GaganDruvakumara/DJ-Controller/CAD Files/3D Print/RotaryEncoderKnob 2x.step

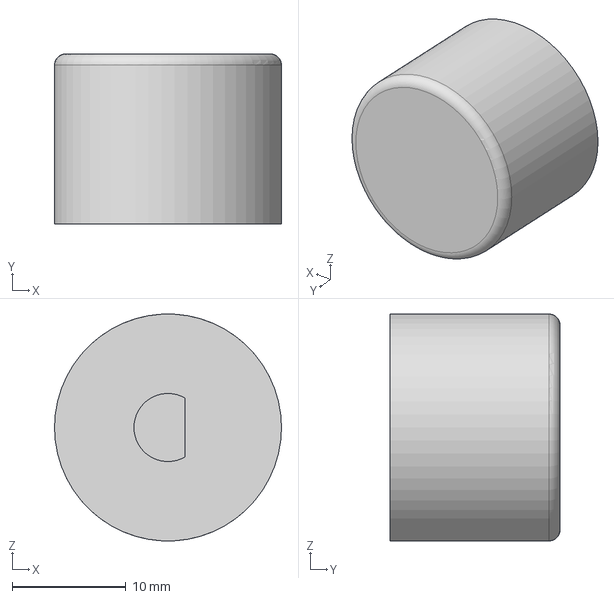
[picture p16: CAD file, 2026-06-20]
CAD Files/3D Print/RotaryEncoderKnob 2x.step
20.0 x 15.0 x 20.0 mm
