GaganDruvakumara/DJ-Controller/CAD Files/PCB 3D Models/JogEncoder.step

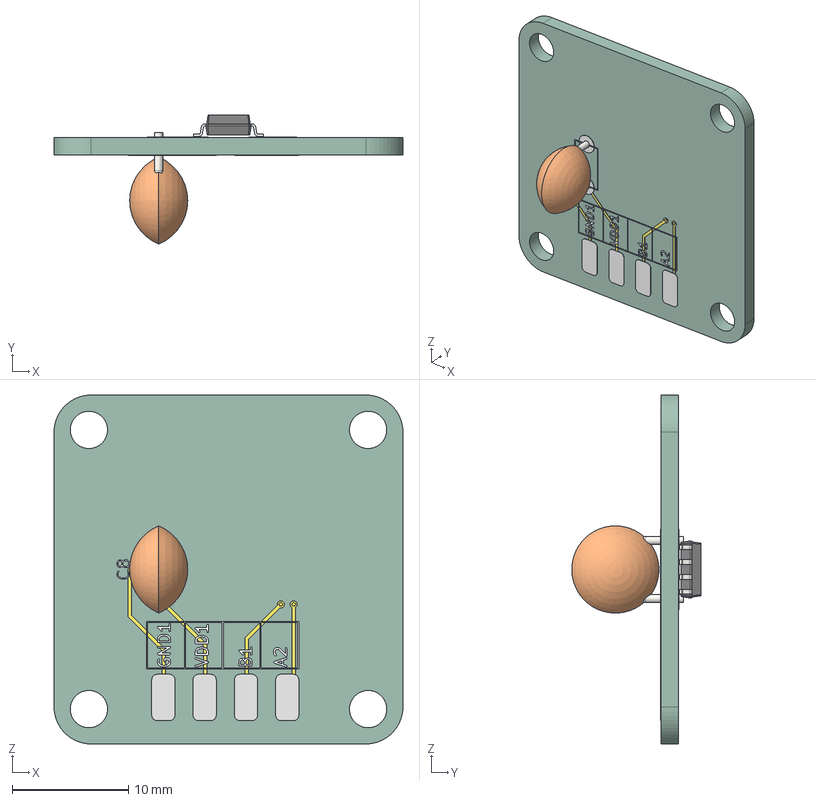
[picture p17: CAD file, 2026-06-20]
CAD Files/PCB 3D Models/JogEncoder.step
30.0 x 11.1 x 30.0 mm
