GaganDruvakumara/DJ-Controller/CAD Files/3D Print/ChCueKeycap 4x.step

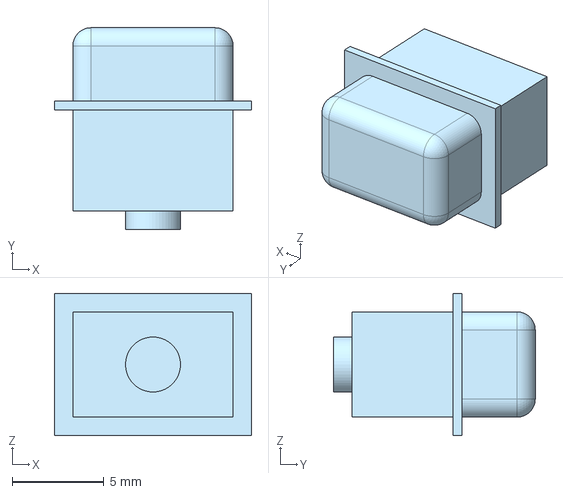
[picture p18: CAD file, 2026-06-20]
CAD Files/3D Print/ChCueKeycap 4x.step
10.8 x 11.0 x 7.75 mm
