GaganDruvakumara/DJ-Controller/CAD Files/3D Print/FaderKnob 7x.step

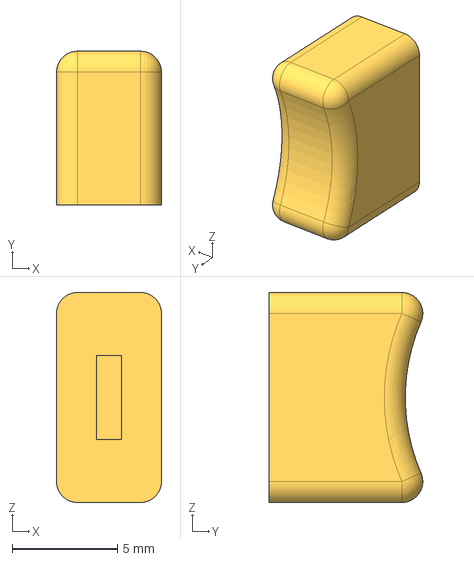
[picture p19: CAD file, 2026-06-20]
CAD Files/3D Print/FaderKnob 7x.step
5.00 x 7.32 x 10.0 mm
