GaganDruvakumara/DJ-Controller/CAD Files/3D Print/PotKnob 24x.step

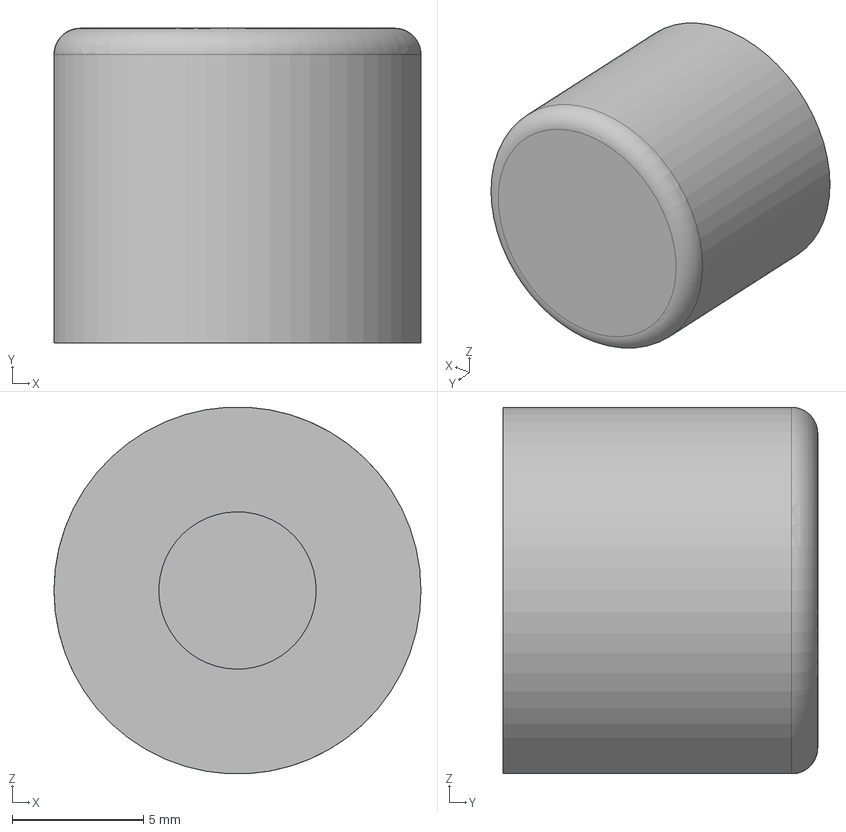
[picture p20: CAD file, 2026-06-20]
CAD Files/3D Print/PotKnob 24x.step
14.0 x 12.0 x 14.0 mm
