GaganDruvakumara/DJ-Controller/CAD Files/3D Print/Jog Wheel 2x.step

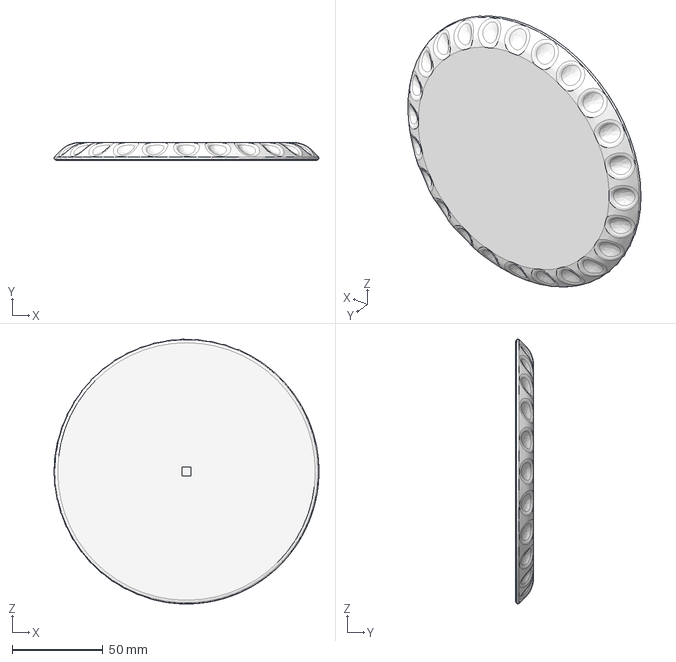
[picture p21: CAD file, 2026-06-20]
CAD Files/3D Print/Jog Wheel 2x.step
146.1 x 10.0 x 146.1 mm
