GaganDruvakumara/DJ-Controller/CAD Files/3D Print/PCBSpacer 2x.step

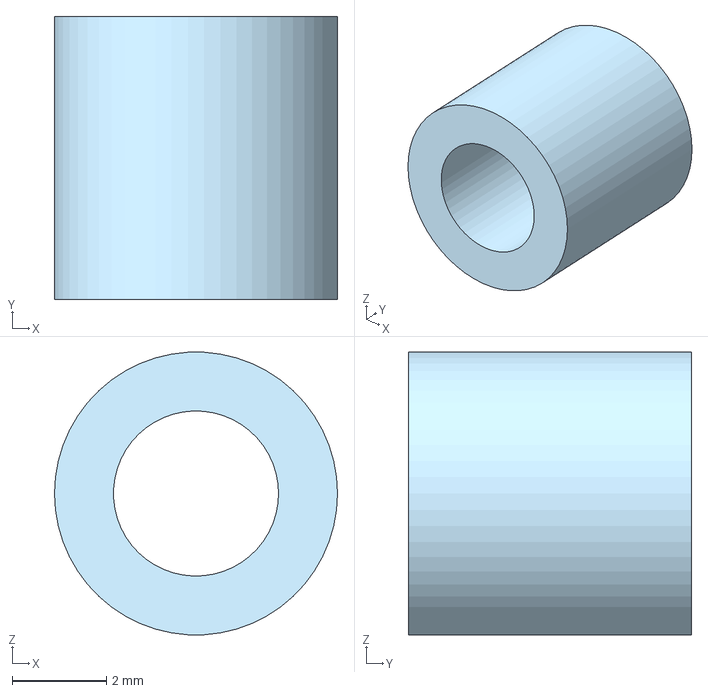
[picture p22: CAD file, 2026-06-20]
CAD Files/3D Print/PCBSpacer 2x.step
6.00 x 6.00 x 5.99 mm
