GaganDruvakumara/DJ-Controller/CAD Files/3D Print/SPDTSWExtender 2x.step

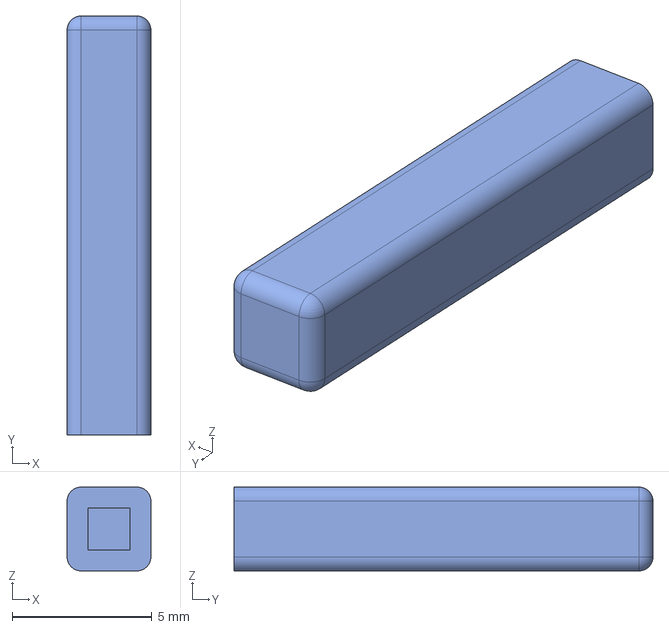
[picture p23: CAD file, 2026-06-20]
CAD Files/3D Print/SPDTSWExtender 2x.step
3.00 x 15.0 x 3.00 mm
