GaganDruvakumara/DJ-Controller/Firmware/definitions.h

#define SDA 0
#define SCL 1


#define JOG1_A 12
#define JOG1_B 13


#define MainExpINT 14
#define Pad1INT 15
#define Pad2INT 16


#define DSSW2 18
#define DSSW4 19


#define LEDL_PIN 20
#define LEDR_PIN 21


#define JOG2_A 22
#define JOG2_B 28


#define MUX_A 26
#define MUX_B 27

#define COM1 0
#define COM2 1
